gerb-ster/TH-566-VCO/images/IMG_3573.jpeg

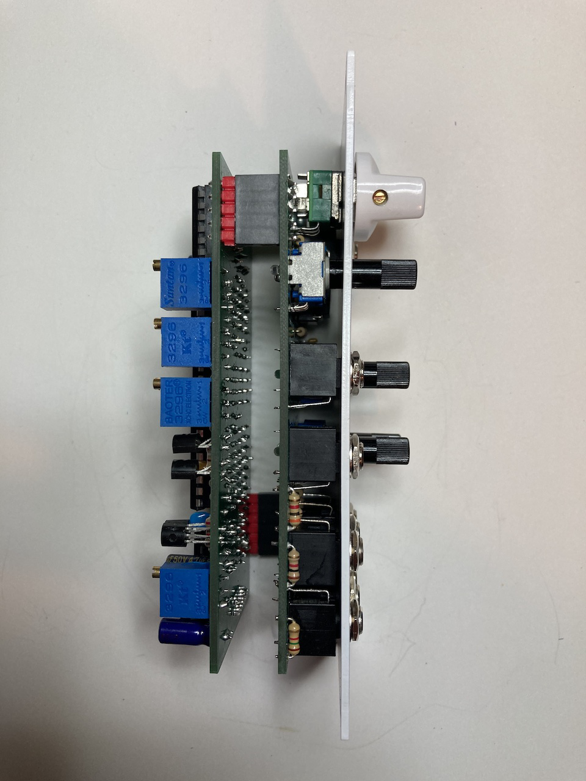
images/IMG_3573.jpeg
