gerb-ster/TH-566-VCO/images/IMG_3574.jpeg

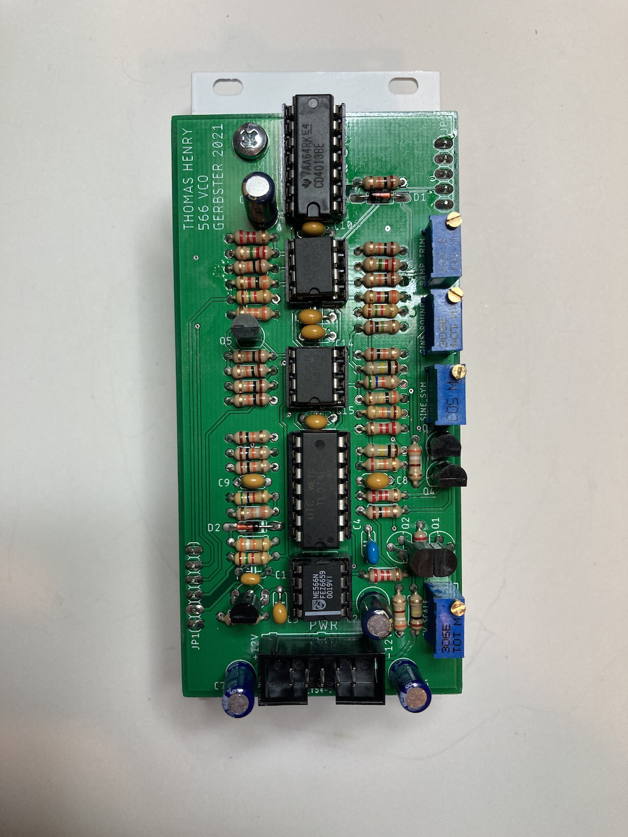
images/IMG_3574.jpeg
