gerb-ster/TH-566-VCO/images/IMG_3575.jpeg

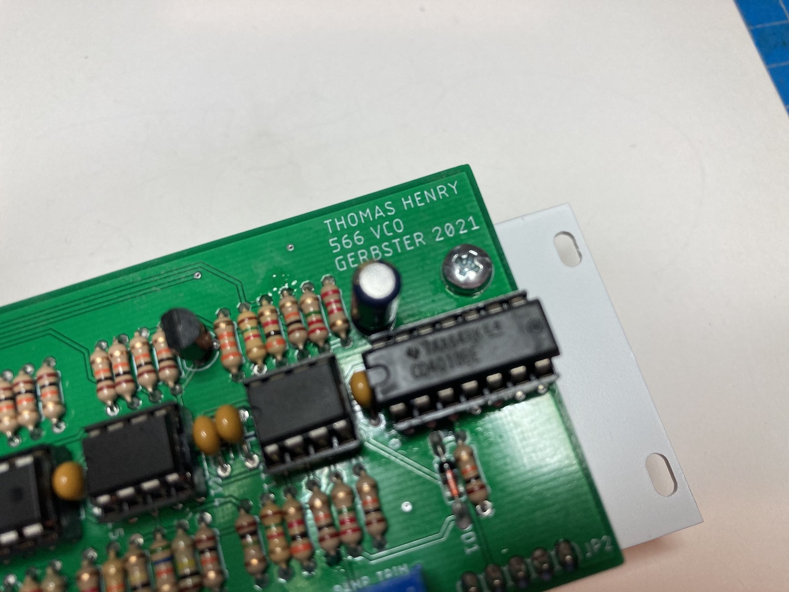
images/IMG_3575.jpeg
