gerb-ster/TH-566-VCO/images/IMG_3576.jpeg

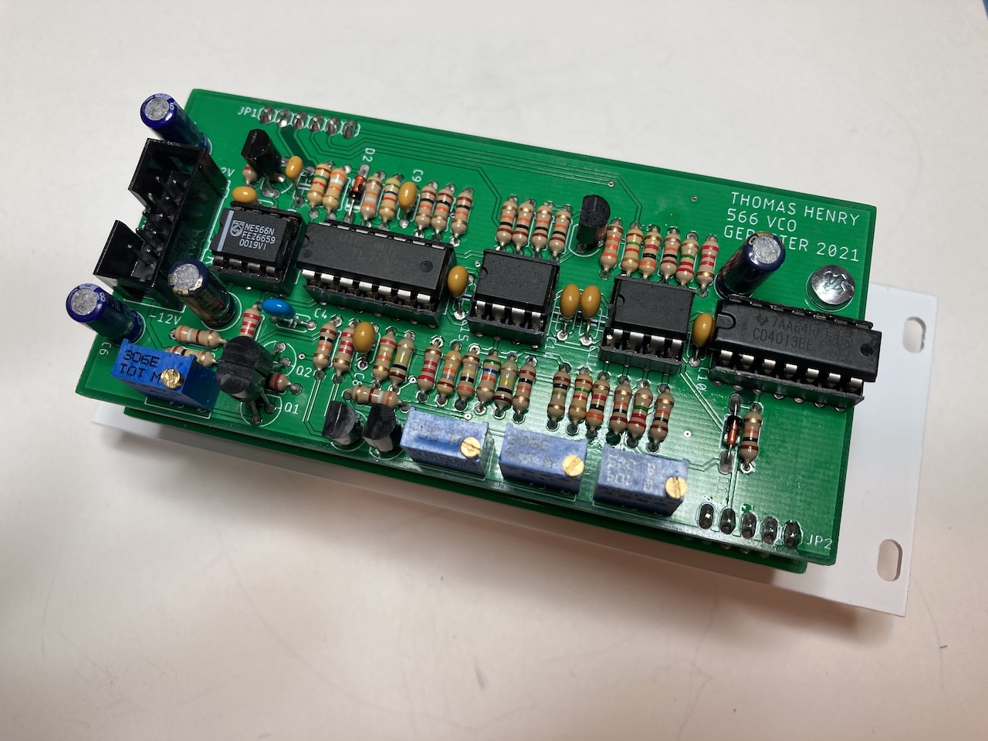
images/IMG_3576.jpeg
