gerb-ster/TH-566-VCO/images/IMG_3577.jpeg

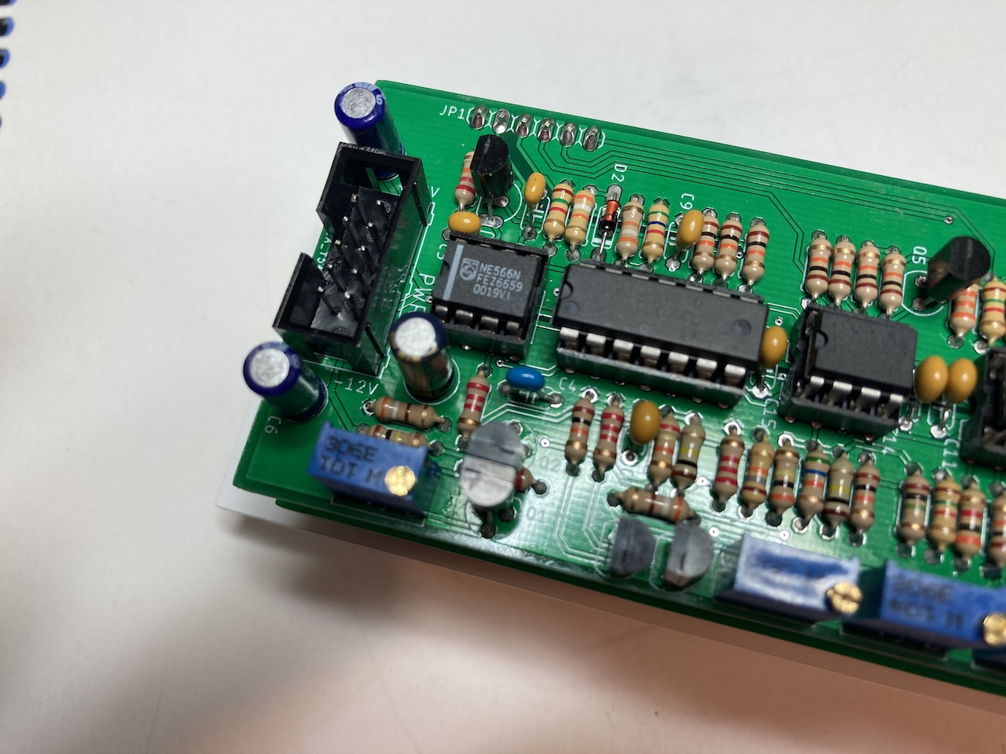
images/IMG_3577.jpeg
