gerb-ster/TH-566-VCO/images/IMG_3578.jpeg

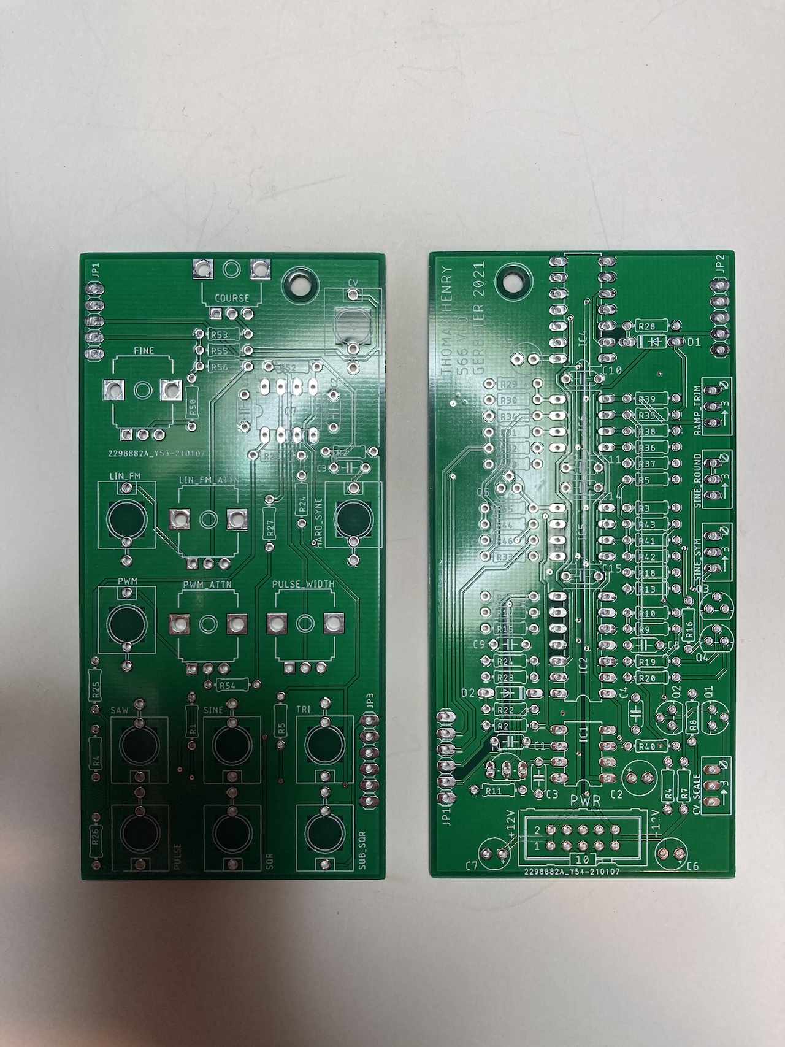
images/IMG_3578.jpeg
