gerb-ster/TH-566-VCO/images/IMG_3579.jpeg

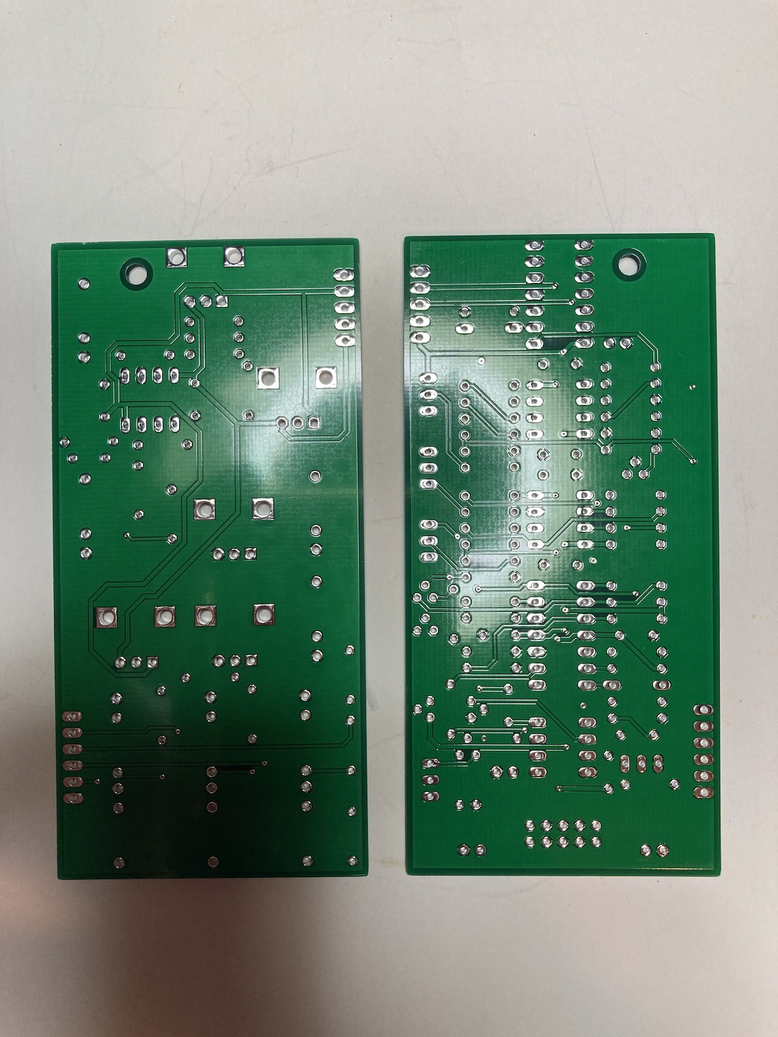
images/IMG_3579.jpeg
