gerb-ster/TH-566-VCO/images/IMG_3580.jpeg

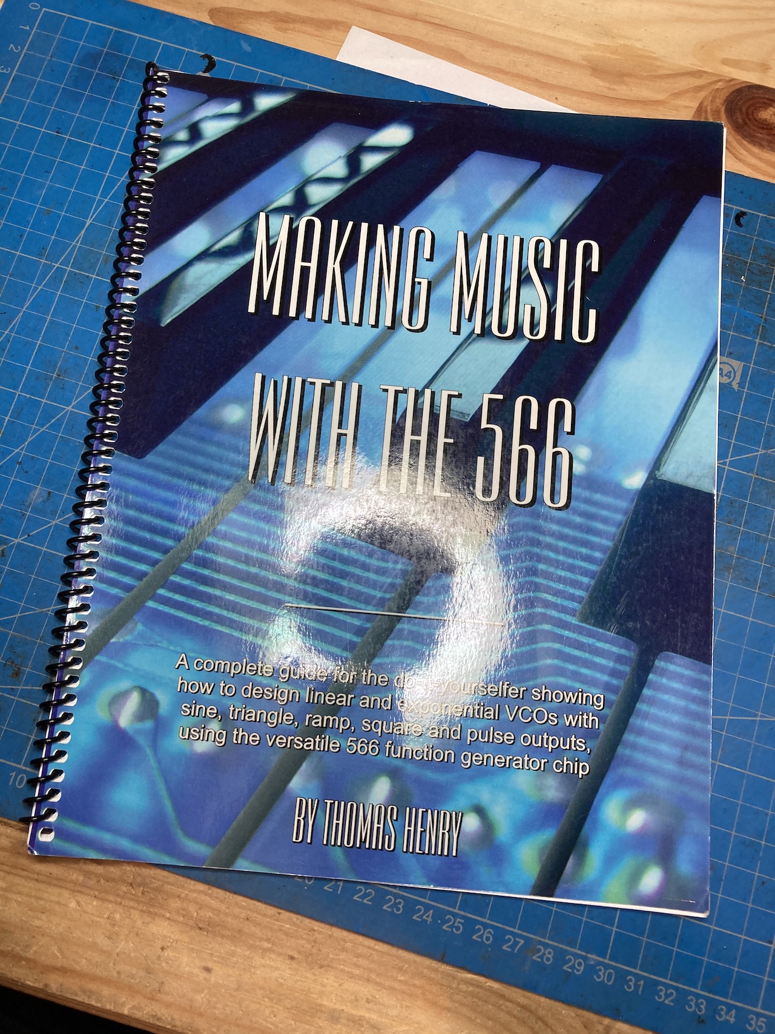
images/IMG_3580.jpeg
