gerb-ster/TH-566-VCO/images/IMG_3581.jpeg

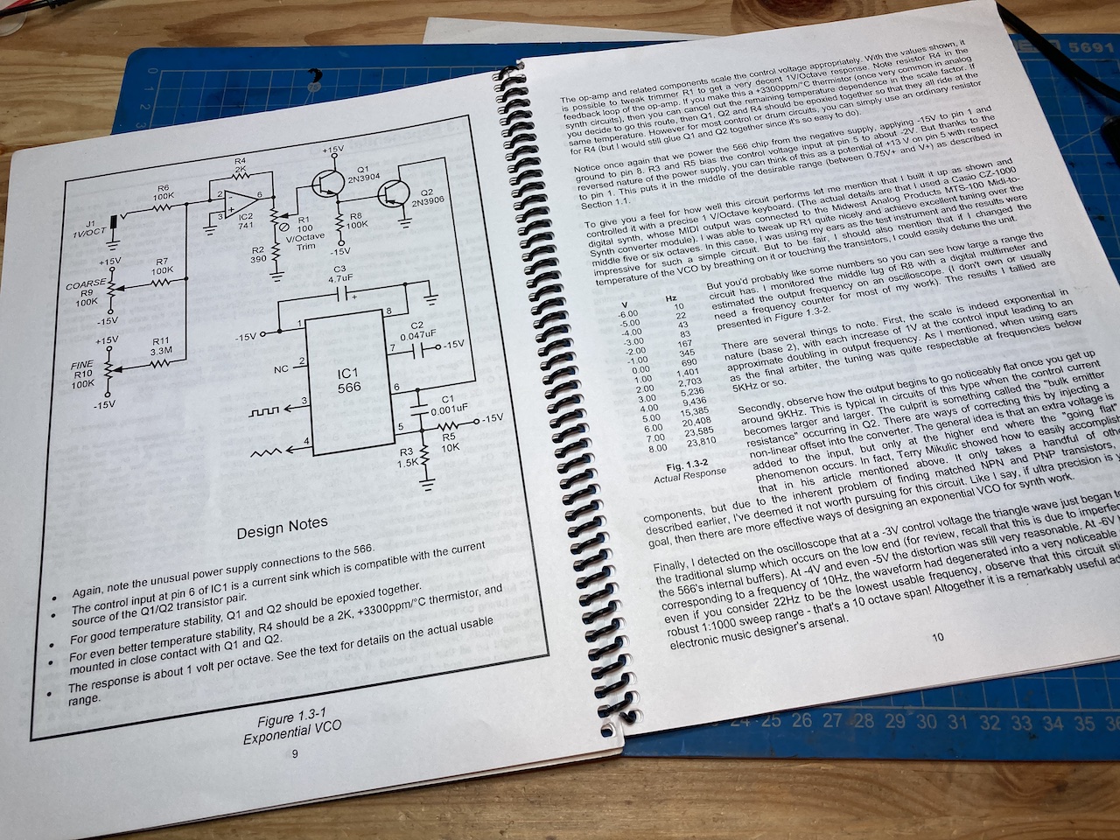
images/IMG_3581.jpeg
