gerb-ster/TH-566-VCO/images/IMG_3582.jpeg

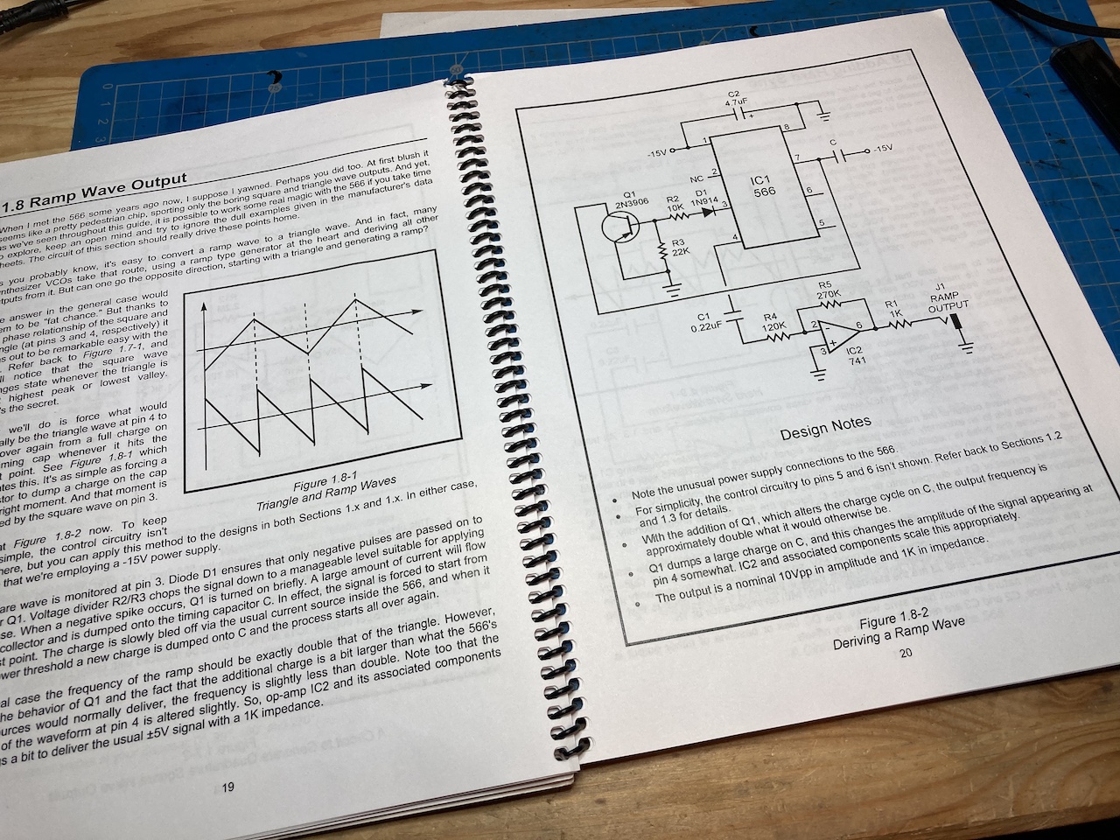
images/IMG_3582.jpeg
