gerb-ster/TH-566-VCO/images/IMG_3583.jpeg

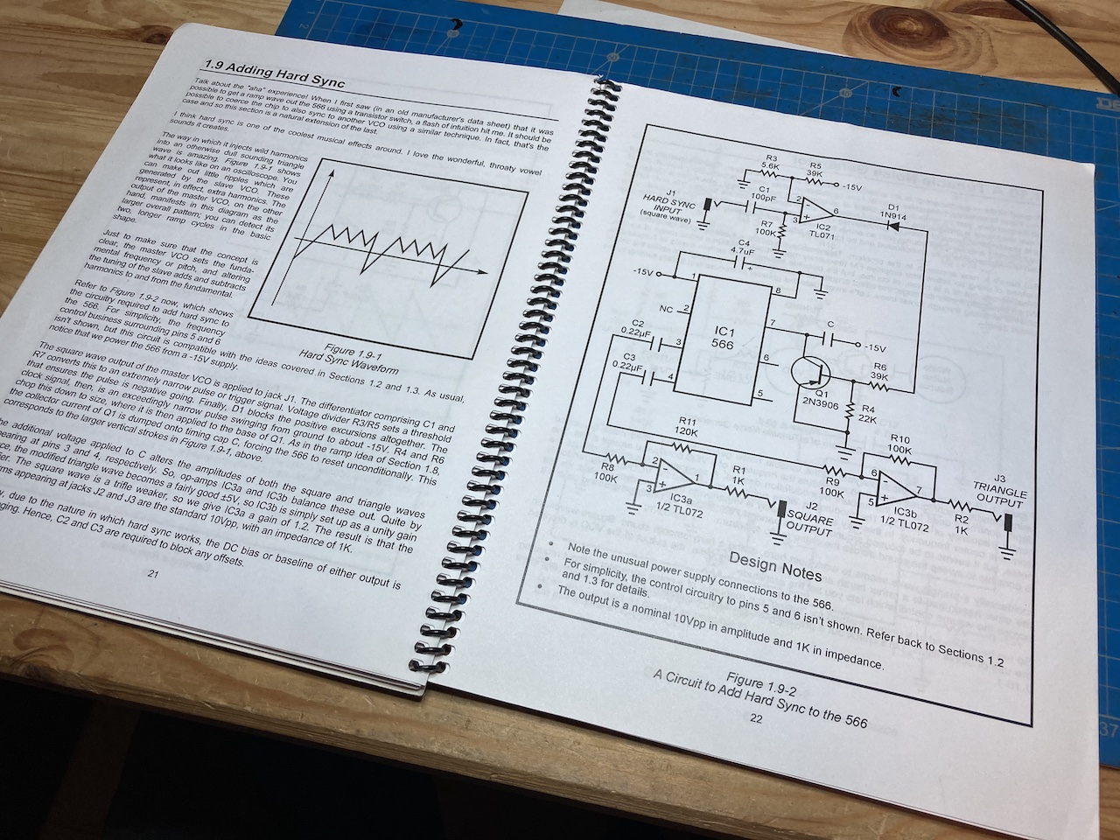
images/IMG_3583.jpeg
